redraw/euclid-16/kicad/euclid-16.kicad_sch

## KiCad design kicad/euclid-16.kicad_sch (2025-06-13, an earlier design)

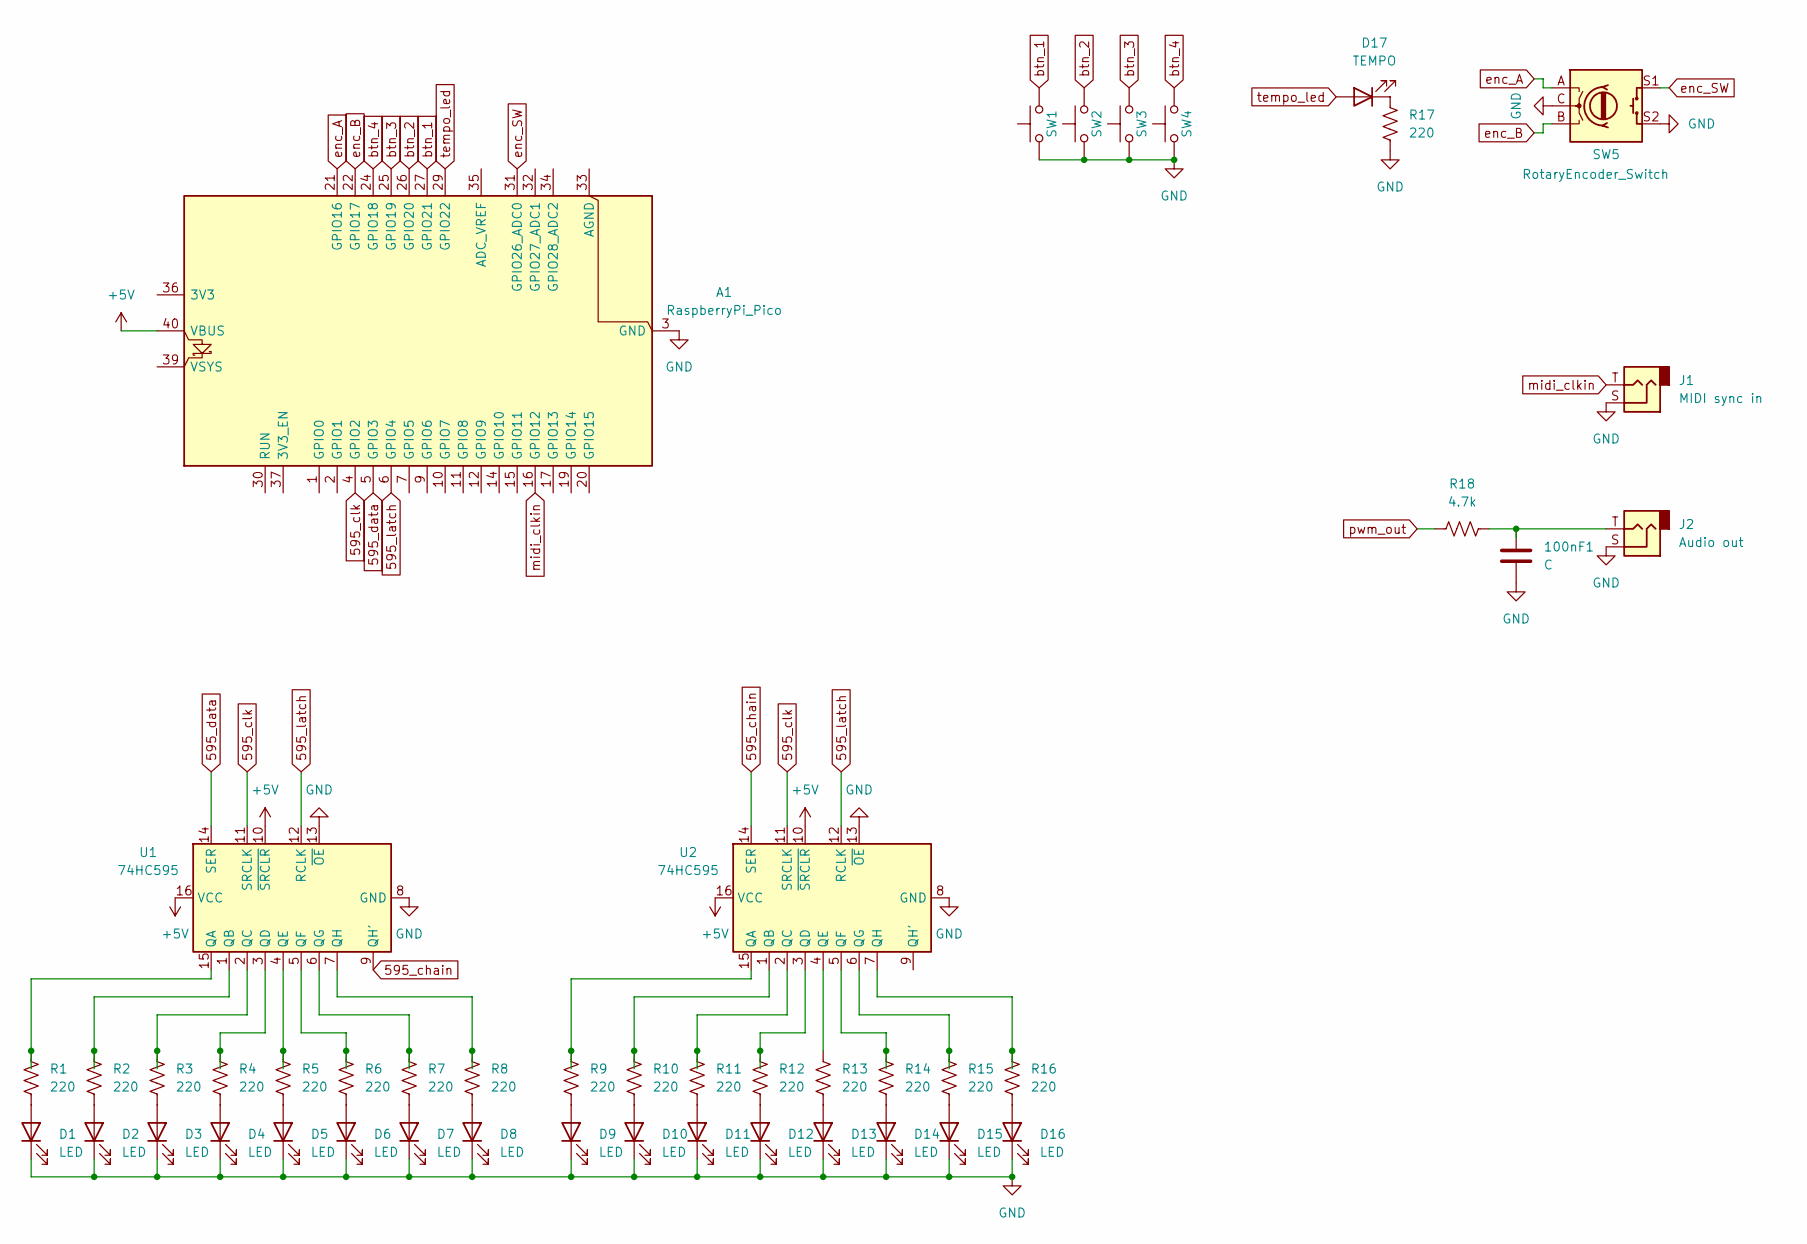
[picture p2: schematic euclid-16.kicad_sch]

Parts:
100nF1: C; C_Disc_D3.0mm_W1.6mm_P2.50mm
A1: RaspberryPi_Pico; RaspberryPi_Pico_Common_Unspecified
D1, D2, D3, D4, D5, D6, D7, D8, D9, D10, D11, D12, D13, D14, D15, D16: LED; LED_D3.0mm
D17: TEMPO; LED_D5.0mm
J1: MIDI sync in; Jack_3.5mm_CUI_SJ1-3525N_Horizontal
J2: Audio out; Jack_3.5mm_CUI_SJ1-3525N_Horizontal
R1, R2, R3, R4, R5, R6, R7, R8, R9, R10, R11, R12, R13, R14, R15, R16, R17: 220; R_Axial_DIN0207_L6.3mm_D2.5mm_P7.62mm_Horizontal
R18: 4.7k; R_Axial_DIN0207_L6.3mm_D2.5mm_P7.62mm_Horizontal
SW1, SW2, SW3, SW4: SW_Push; SW_PUSH_6mm
SW5: RotaryEncoder_Switch; RotaryEncoder_Alps_EC11E-Switch_Vertical_H20mm
U1, U2: 74HC595; DIP-16_W7.62mm_Socket

Connections:
595_chain: U1.9 (QH'), U2.14 (SER)
595_clk: A1.4 (GPIO2), U1.11 (SRCLK), U2.11 (SRCLK)
595_data: A1.5 (GPIO3), U1.14 (SER)
595_latch: A1.6 (GPIO4), U1.12 (RCLK), U2.12 (RCLK)
+5V: A1.40 (VBUS), U1.10 (~SRCLR), U1.16 (VCC), U2.10 (~SRCLR), U2.16 (VCC)
GND: 100nF1.2, A1.3 (GND), A1.8 (GND), A1.13 (GND), A1.18 (GND), A1.23 (GND), A1.28 (GND), A1.38 (GND), D1.1 (K), D2.1 (K), D3.1 (K), D4.1 (K), D5.1 (K), D6.1 (K), D7.1 (K), D8.1 (K), D9.1 (K), D10.1 (K), D11.1 (K), D12.1 (K), D13.1 (K), D14.1 (K), D15.1 (K), D16.1 (K), J1.S, J2.S, R17.1, SW1.1, SW2.1, SW3.1, SW4.1, SW5.C, SW5.S2, U1.8 (GND), U1.13 (~OE), U2.8 (GND), U2.13 (~OE)
unnamed: 100nF1.1, J2.T, R18.1
unnamed: D1.2 (A), R1.2
unnamed: D2.2 (A), R2.2
unnamed: D3.2 (A), R3.2
unnamed: D4.2 (A), R4.2
unnamed: D5.2 (A), R5.2
unnamed: D6.2 (A), R6.2
unnamed: D7.2 (A), R7.2
unnamed: D8.2 (A), R8.2
unnamed: D9.2 (A), R9.2
unnamed: D10.2 (A), R10.2
unnamed: D11.2 (A), R11.2
unnamed: D12.2 (A), R12.2
unnamed: D13.2 (A), R13.2
unnamed: D14.2 (A), R14.2
unnamed: D15.2 (A), R15.2
unnamed: D16.2 (A), R16.2
unnamed: D17.1 (K), R17.2
unnamed: R1.1, U1.15 (QA)
unnamed: R2.1, U1.1 (QB)
unnamed: R3.1, U1.2 (QC)
unnamed: R4.1, U1.3 (QD)
unnamed: R5.1, U1.4 (QE)
unnamed: R6.1, U1.5 (QF)
unnamed: R7.1, U1.6 (QG)
unnamed: R8.1, U1.7 (QH)
unnamed: R9.1, U2.15 (QA)
unnamed: R10.1, U2.1 (QB)
unnamed: R11.1, U2.2 (QC)
unnamed: R12.1, U2.3 (QD)
unnamed: R13.1, U2.4 (QE)
unnamed: R14.1, U2.5 (QF)
unnamed: R15.1, U2.6 (QG)
unnamed: R16.1, U2.7 (QH)
btn_1: A1.27 (GPIO21), SW1.2
btn_2: A1.26 (GPIO20), SW2.2
btn_3: A1.25 (GPIO19), SW3.2
btn_4: A1.24 (GPIO18), SW4.2
enc_A: A1.21 (GPIO16), SW5.A
enc_B: A1.22 (GPIO17), SW5.B
enc_SW: A1.31 (GPIO26_ADC0), SW5.S1
midi_clkin: A1.16 (GPIO12), J1.T
pwm_out: R18.2
tempo_led: A1.29 (GPIO22), D17.2 (A)
